MakeICT/electronic-door/door-client/software/python/enroll.py

#!/usr/bin/python
# -*- coding: utf-8 -*-
'''
MakeICT/Bluebird Arthouse Electronic Door Entry

enroll.py: Enrolls a user
Usage: enroll.py [userID [rfid]]

Authors:
	Dominic Canare <dom@greenlightgo.org>
	Rye Kennedy <ryekennedy@gmail.com>
	Christian Kindel <iceman81292@gmail.com>
'''
#@TODO: define error status codes here (duplicate key error)

import os, sys, signal, time, subprocess, argparse, logging, logging.config, yaml
from backend import backend
from get_user import getUser
from cli_helper import *
from MySQLdb import IntegrityError

Dir = os.path.realpath(os.path.dirname(__file__))
doorLockPipedLog = os.path.join(Dir, '../logs/piped-door-lock.log')
config = os.path.join(Dir, 'config.yml')
global_config = yaml.load(file(config, 'r'))
logging.config.dictConfig(global_config['logging'])
log = logging.getLogger('enroll')

def enroll(userID=None, nfcID=None, steal=False, quiet=False, reader=False):
	if os.geteuid() != 0:
		print "Root is required to run this script"
		return

	user = getUser(userID, confirm=(False if userID else True))
	if user == None:
		return
	userID = user['userID']
	
	if not reader:
		if not nfcID:
			putMessage(       "Enter key UID manually,")
			choice = getInput("or read key from NFC reader?", options=['m', 'r'])
			if choice == 'm':
				nfcID = getInput("Enter key UID")
	if not nfcID:
		try:
			restartDoorLock = True if killDoorLock() == 0 else False
			from rpi import interfaceControl
			while True:
				log.debug("Starting NFC read")
				if not quiet:
					putMessage("Swipe card now")
				retry = 0
				while retry < 30:
					interfaceControl.setPowerStatus(True)
					nfcID = interfaceControl.nfcGetUID()
					interfaceControl.setPowerStatus(False)
					if nfcID:
						break
					time.sleep(0.75)
					retry += 1
				log.debug("Finished NFC read")
				if not nfcID and not quiet:
					retry = getInput("Couldn't read card. Retry?", options=['y', 'n'])
					if nfcID != None or retry != 'y':
						break
				else:
					break
		
		except KeyboardInterrupt:
			log.info("Received KeyboardInterrupt")

		except:
			putMessage("Unexpected error: {:}".format(sys.exc_info()[0]),
				   level=severity.ERROR)
			log.error("Unexpected error: {:}".format(sys.exc_info()[0]))
			raise

		finally:
			interfaceControl.cleanup()
			if restartDoorLock:
				log.info("restarting door-lock.py")
				startDoorLock()
	if nfcID != None:
		# @TODO: catch duplicate key error, exit with error status
		try:
			backend.enroll(nfcID, userID, steal)
			putMessage("User [{:d}] enrolled with ID: {:s}".format(userID, nfcID),level=severity.OK)
		except IntegrityError:
			putMessage("Key is already assigned!",level=severity.WARNING)
			putMessage("User not enrolled",level=severity.ERROR)
	else:
		putMessage("Did not enroll user", level=severity.WARNING)

def killDoorLock():
	process = subprocess.Popen(['pgrep', 'door-lock.py'], stdout=subprocess.PIPE)
	out, err = process.communicate()
	if out != '':
		log.debug('Killing door-lock.py')
		subprocess.call(['stop','door-lock'])
		time.sleep(1)
		try:
			if os.kill(int(out), 0) == None:	#TODO: use upstart status?
				log.error('Could not kill door-lock.py')
				log.error('Exiting')
				return -1	#@TODO:define error codes
			else:
				return 0
				log.debug('Successfully killed door-lock.py')
		except OSError:
			return 0
			log.debug('Successfully killed door-lock.py')
	else:
		return 1

def startDoorLock():
	#FNULL = open(os.devnull, 'w')
	FNULL = open(doorLockPipedLog, 'a')
	log.debug('Restarting door-lock.py')
	subprocess.Popen(['start','door-lock'],
			 stdout=FNULL, stderr=subprocess.STDOUT)
	restartDoorLock = False



if __name__ == "__main__":
	log.info("==========[enroll.py started]==========")

	parser = argparse.ArgumentParser(description='Add an NFC ID to a user in the MakeICT database.')
	parser.add_argument("-u", "--userid", help="The user's unique userID.", type=int)
	parser.add_argument("-s", "--steal", help="Re-assign the card if it is already registered to another user.", action="store_true")
	parser.add_argument("-q", "--quiet", help="Suppress prompts and output", action="store_true")
	method = parser.add_mutually_exclusive_group()
	method.add_argument("-n", "--nfcid", help="UID of the user's NFC card.")
	method.add_argument("-r", "--reader", help="Read a card UID from the card reader", action="store_true")
	args = parser.parse_args()
	try:
		enroll(args.userid, args.nfcid, args.steal, args.quiet, args.reader)
	except KeyboardInterrupt:
		pass
